MZachmann/PicoPendant/PythonSrc/display/colorSet.py

# color is 5-6-5 stored


DarkTheme = {
	'background' : 0x021,
	'foreground' : 0x7fff,
	'highlight' : 0x0088
	}

LightTheme = {
	'background' : 0xffff,
	'foreground' : 0x021,
	'highlight' : 0x01f
	}

SolidClr = { 
	'red' 	: 0x07e0,
	'green' : 0x001f,
	'blue' 	: 0xf800,
	'darkblue' : 0x0e00,
	'white' : 0xffff,
	'yellow'   : 0x07ff,
	'dkyellow' : 0x0088,
	'black'    : 0,
	'gray'     : 0x1863,
	'darkred'  : 0x01e0,
	'darkgreen' : 0x04
	}
